vongomben/smart-foot-brace/img/data-from-students/four.jpeg

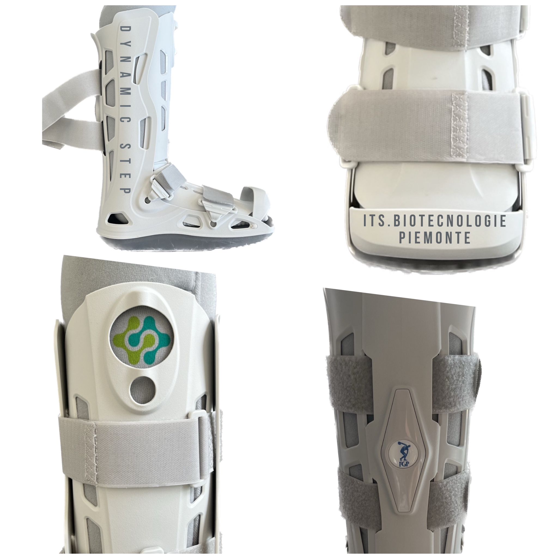
img/data-from-students/four.jpeg
