vongomben/smart-foot-brace/img/data-from-students/front.jpeg

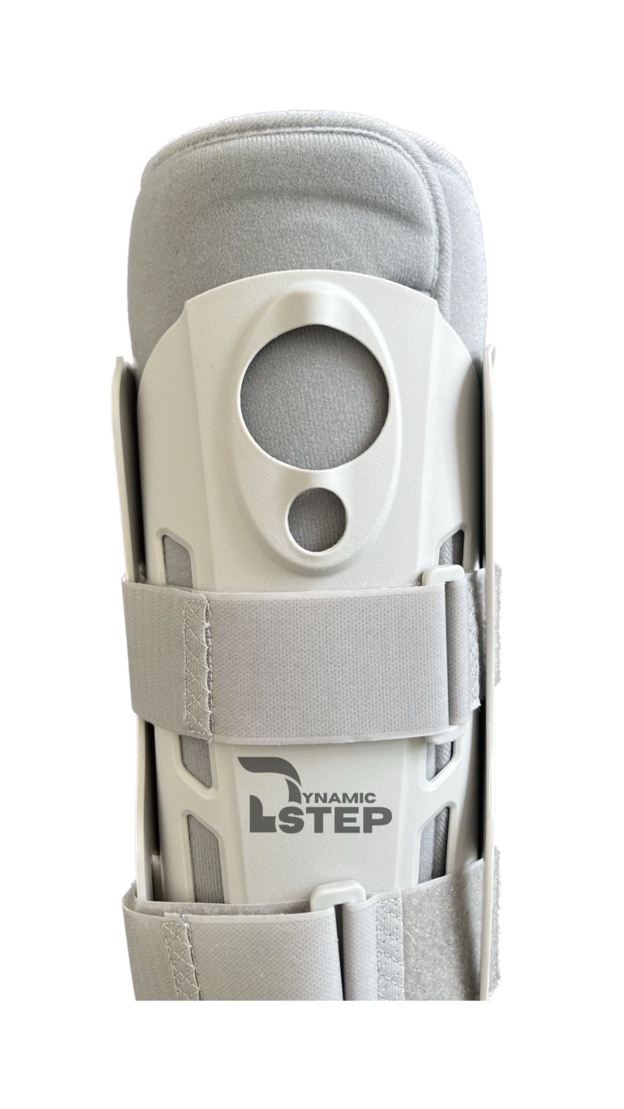
img/data-from-students/front.jpeg
