vongomben/smart-foot-brace/img/review-13-oct/4.png

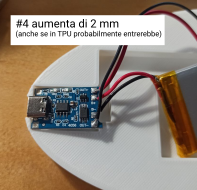
img/review-13-oct/4.png
