vongomben/smart-foot-brace/img/review-13-oct/9.png

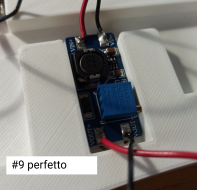
img/review-13-oct/9.png
