vongomben/smart-foot-brace/img/review-13-oct/63.png

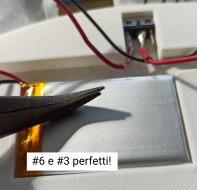
img/review-13-oct/63.png
