vongomben/smart-foot-brace/img/review-13-oct/Final.png

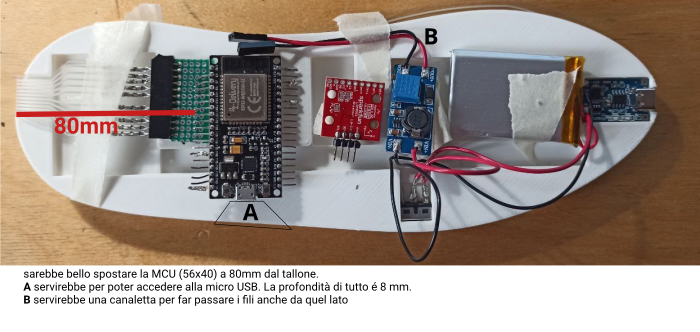
img/review-13-oct/Final.png
