vongomben/smart-foot-brace/img/maker-faire.png

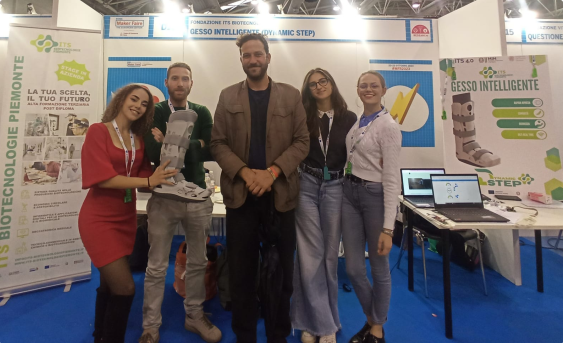
img/maker-faire.png
