vongomben/smart-foot-brace/img/review-13-oct/problem.png

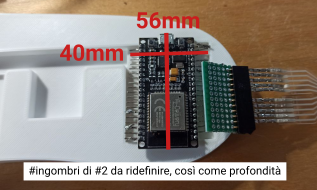
img/review-13-oct/problem.png
